emb3rcia/spark-tboi/Firmware/spark-tboi/Core/Inc/functions.h

//
// Created by ember on 15.03.2026.
//

#ifndef SPARK_TBOI_FUNCTIONS_H
#define SPARK_TBOI_FUNCTIONS_H

void handleEncoder();
void updateOLED();
uint16_t handleDescriptor();

#endif //SPARK_TBOI_FUNCTIONS_H
